afms135/signl/Hardware/Render_back.png

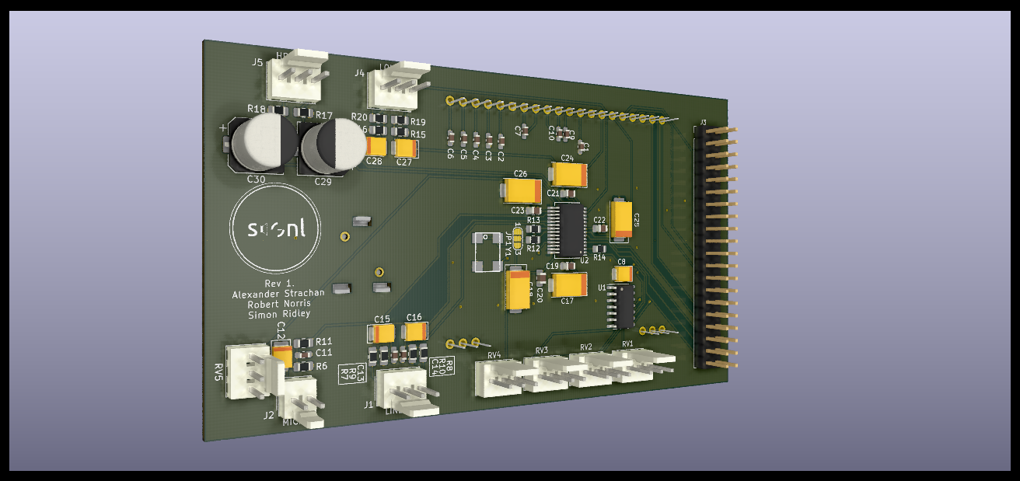
Hardware/Render_back.png
