afms135/signl/Hardware/Render_front.png

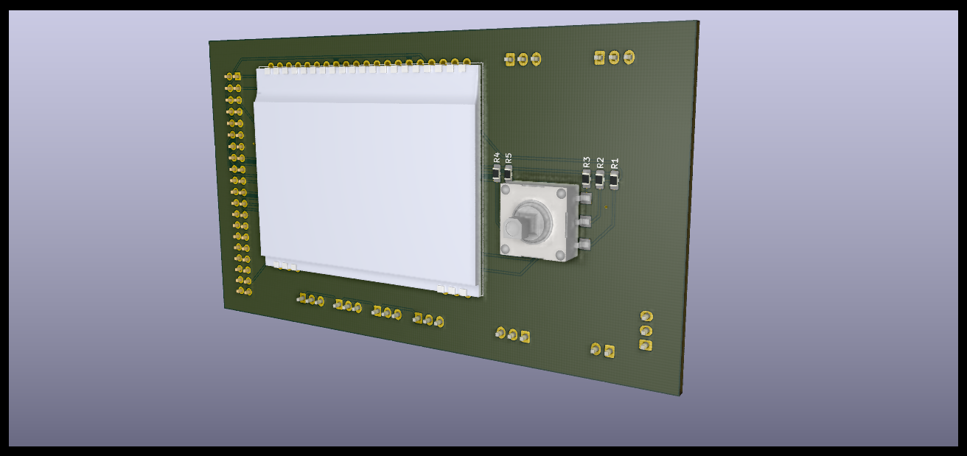
Hardware/Render_front.png
