afms135/signl/Hardware/RenderBackPerp.png

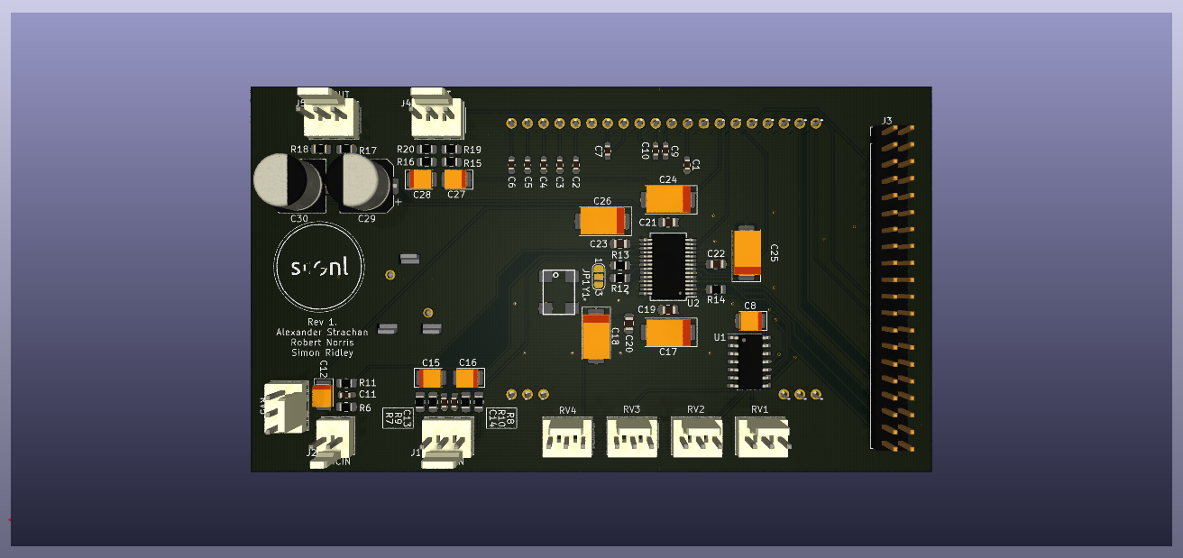
Hardware/RenderBackPerp.png
