afms135/signl/Hardware/RenderFrontPerp.png

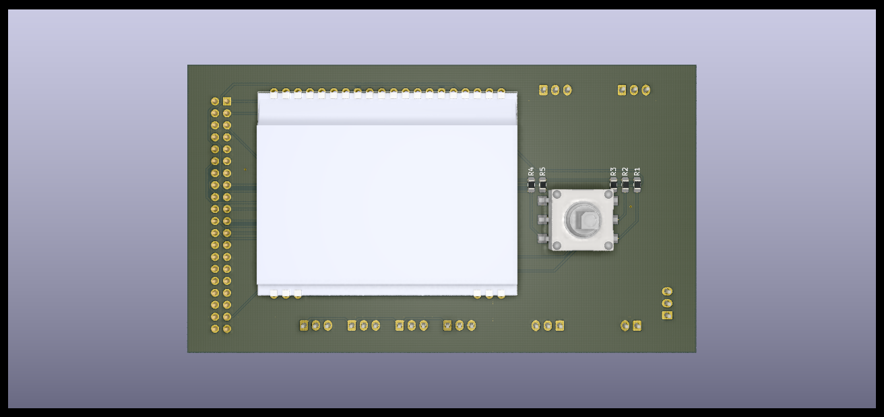
Hardware/RenderFrontPerp.png
