afms135/signl/Media/audio_interface.png

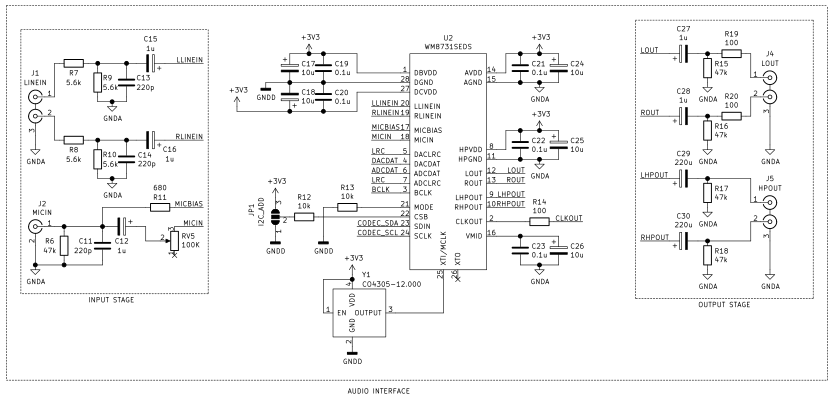
Media/audio_interface.png
