afms135/signl/Media/BlockDiagram.png

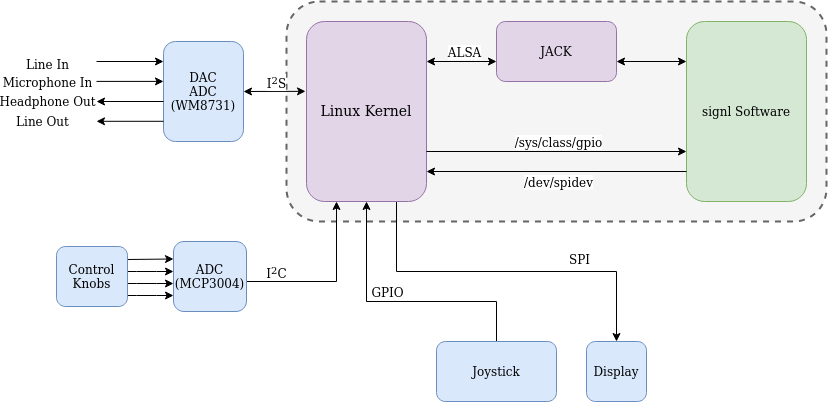
Media/BlockDiagram.png
