afms135/signl/Media/BoxRender.png

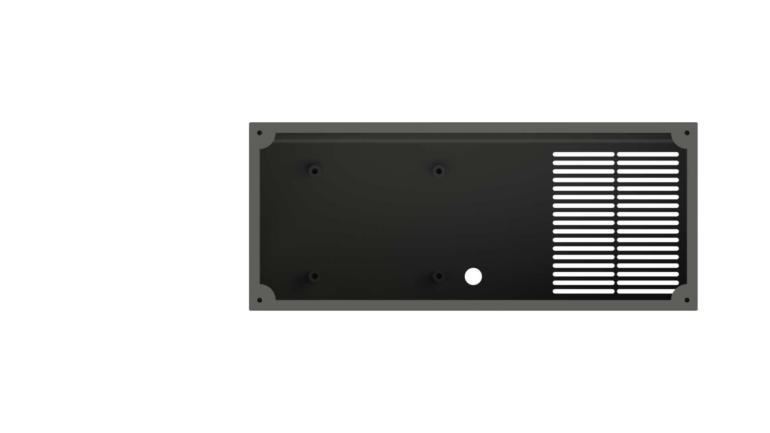
Media/BoxRender.png
