afms135/signl/Media/class_diag.png

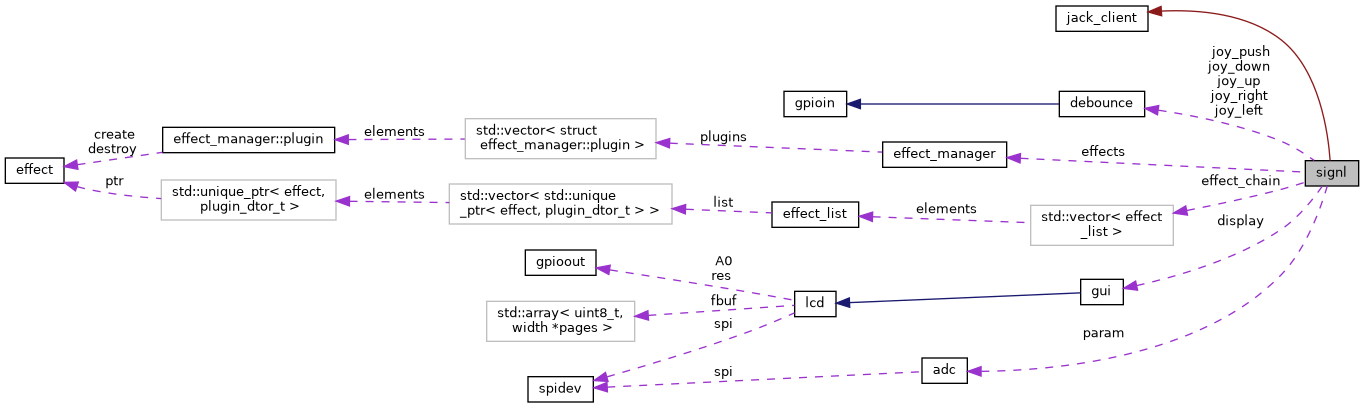
Media/class_diag.png
