afms135/signl/Media/effect_chain.png

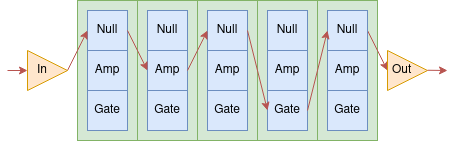
Media/effect_chain.png
