afms135/signl/Media/eqgraph.png

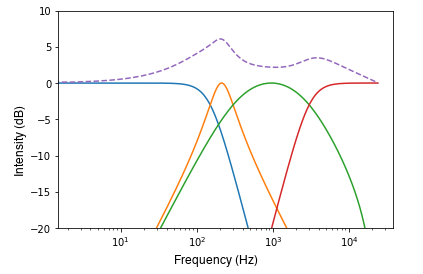
Media/eqgraph.png
