afms135/signl/Media/faceplate_dimensions.png

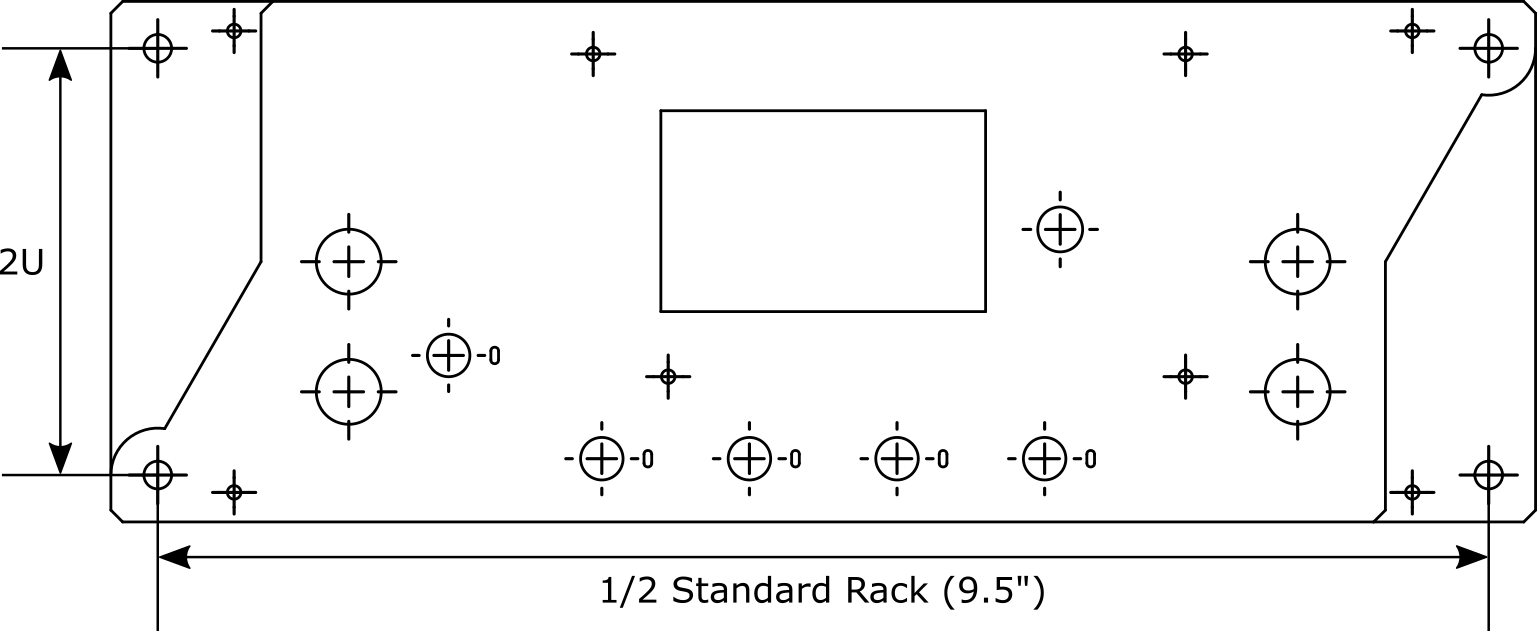
Media/faceplate_dimensions.png
