afms135/signl/Media/FullRender.png

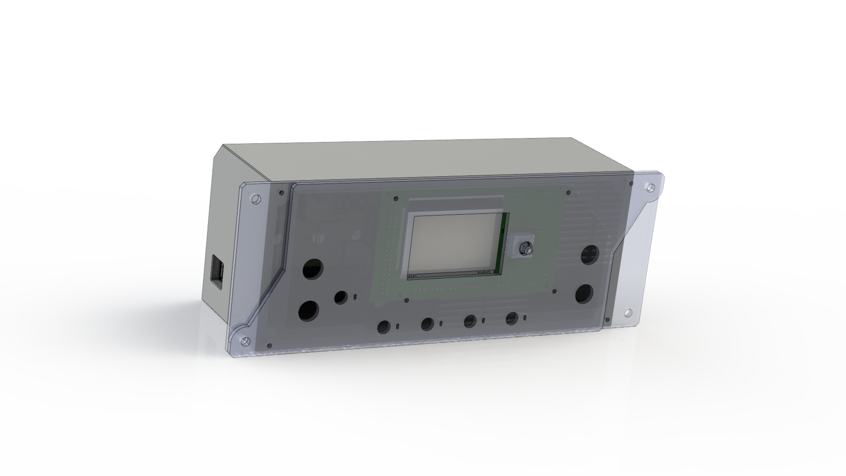
Media/FullRender.png
