afms135/signl/Media/gui_photos.jpg

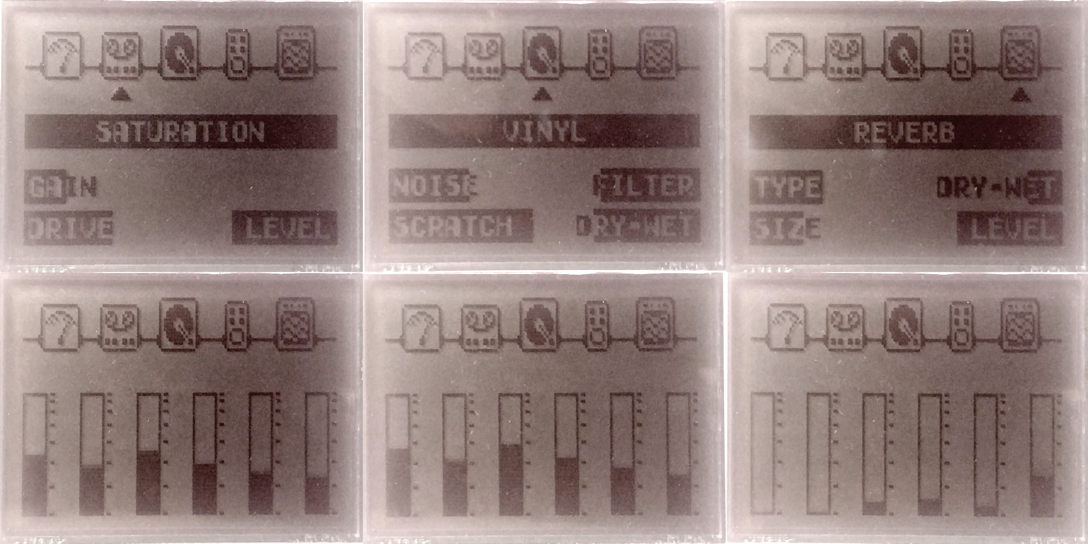
Media/gui_photos.jpg
