afms135/signl/Media/human_interface.png

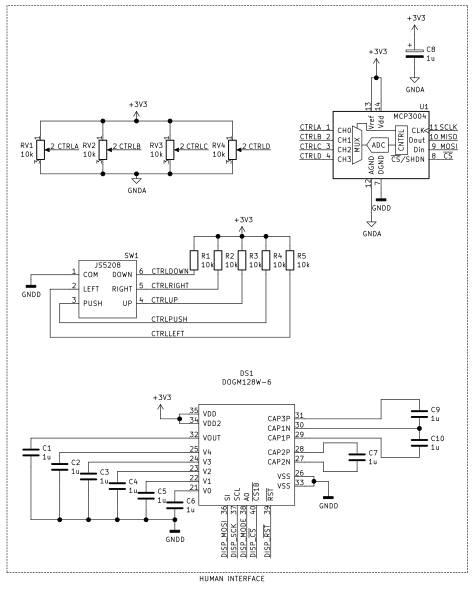
Media/human_interface.png
