afms135/signl/Media/Latencytest1.png

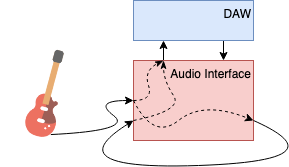
Media/Latencytest1.png
