afms135/signl/Media/Latencytest2.png

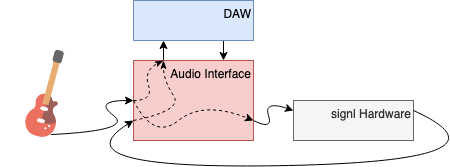
Media/Latencytest2.png
