afms135/signl/Media/PCBreal.jpeg

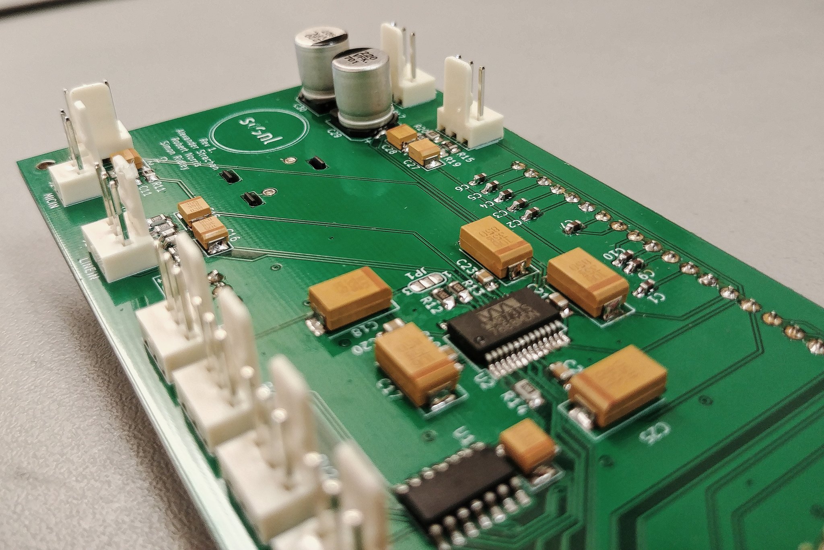
Media/PCBreal.jpeg
