afms135/signl/Media/PCBreal_front.jpeg

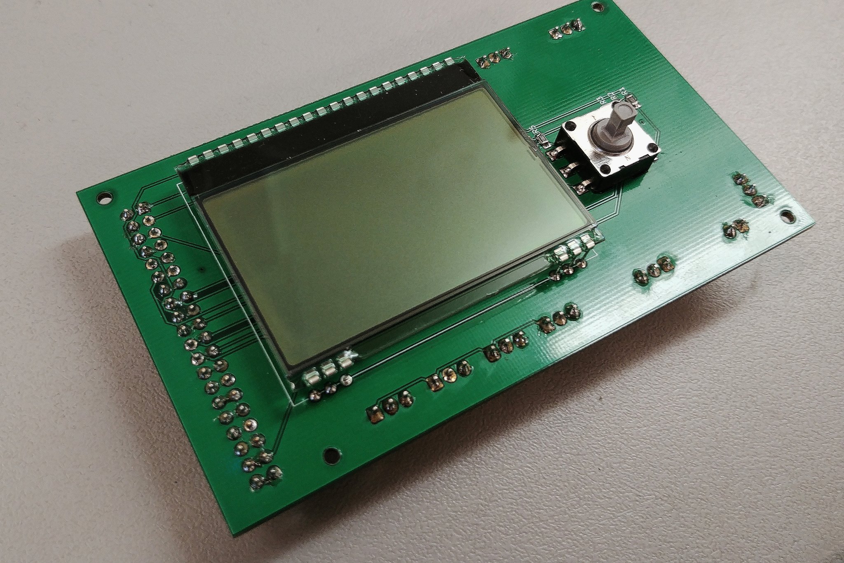
Media/PCBreal_front.jpeg
