afms135/signl/Media/software.png

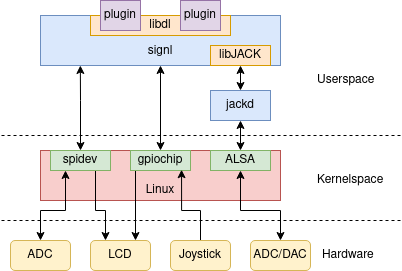
Media/software.png
