afms135/signl/Media/Video Thumbnails/eq.png

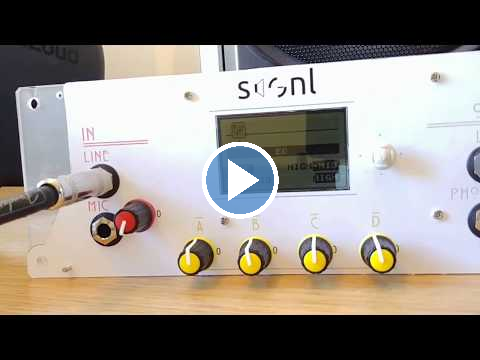
Media/Video Thumbnails/eq.png
