afms135/signl/Media/Video Thumbnails/guitartrack.png

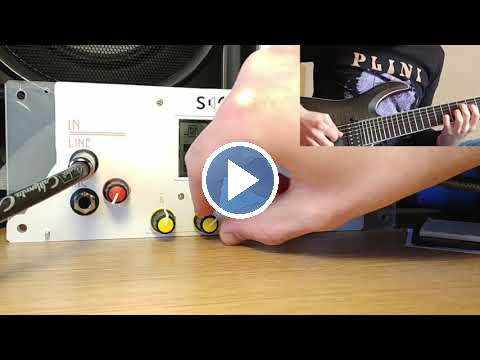
Media/Video Thumbnails/guitartrack.png
