afms135/signl/Media/Video Thumbnails/lofi.png

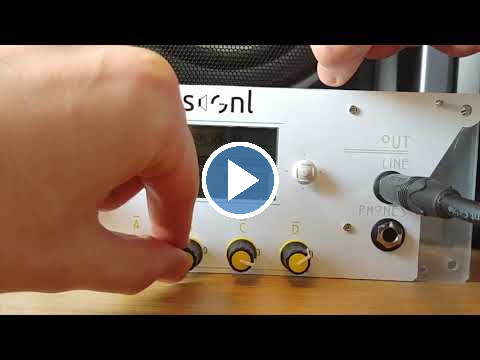
Media/Video Thumbnails/lofi.png
