afms135/signl/Media/Video Thumbnails/naivetuner.png

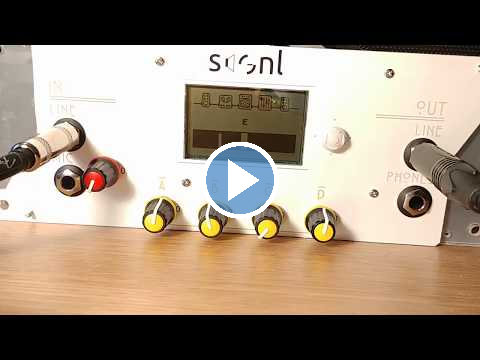
Media/Video Thumbnails/naivetuner.png
