afms135/signl/Media/Video Thumbnails/reverb.png

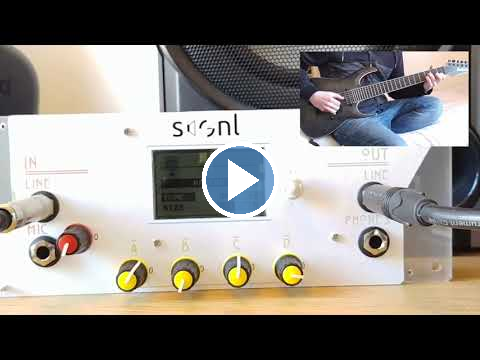
Media/Video Thumbnails/reverb.png
