afms135/signl/Media/Video Thumbnails/saturation.png

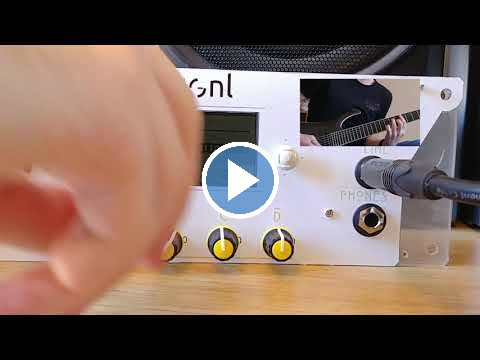
Media/Video Thumbnails/saturation.png
