afms135/signl/Media/Video Thumbnails/tremolo.png

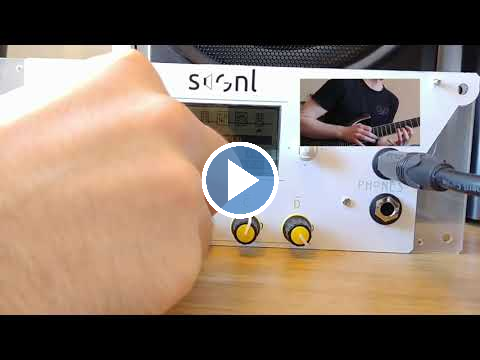
Media/Video Thumbnails/tremolo.png
