afms135/signl/Media/Video Thumbnails/tuner.png

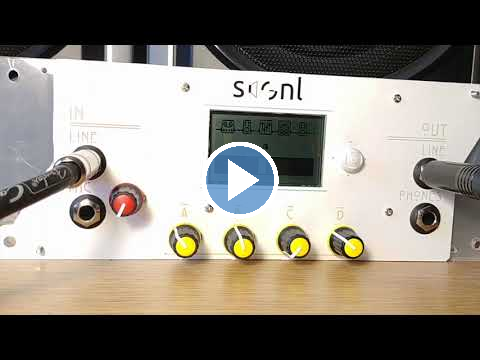
Media/Video Thumbnails/tuner.png
