afms135/signl/Media/Video Thumbnails/vinyl.png

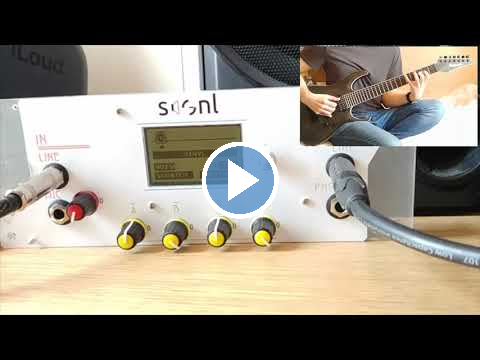
Media/Video Thumbnails/vinyl.png
