afms135/signl/Media/MidAssembly.jpg

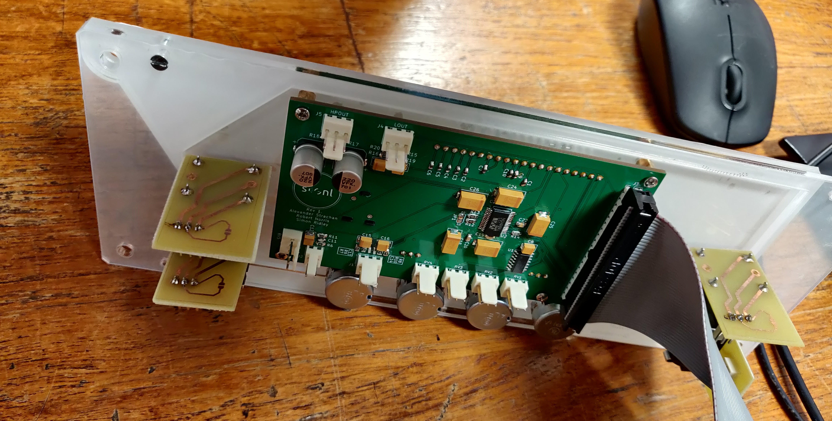
Media/MidAssembly.jpg
