afms135/signl/Media/Testing/Noise Gate/A.png

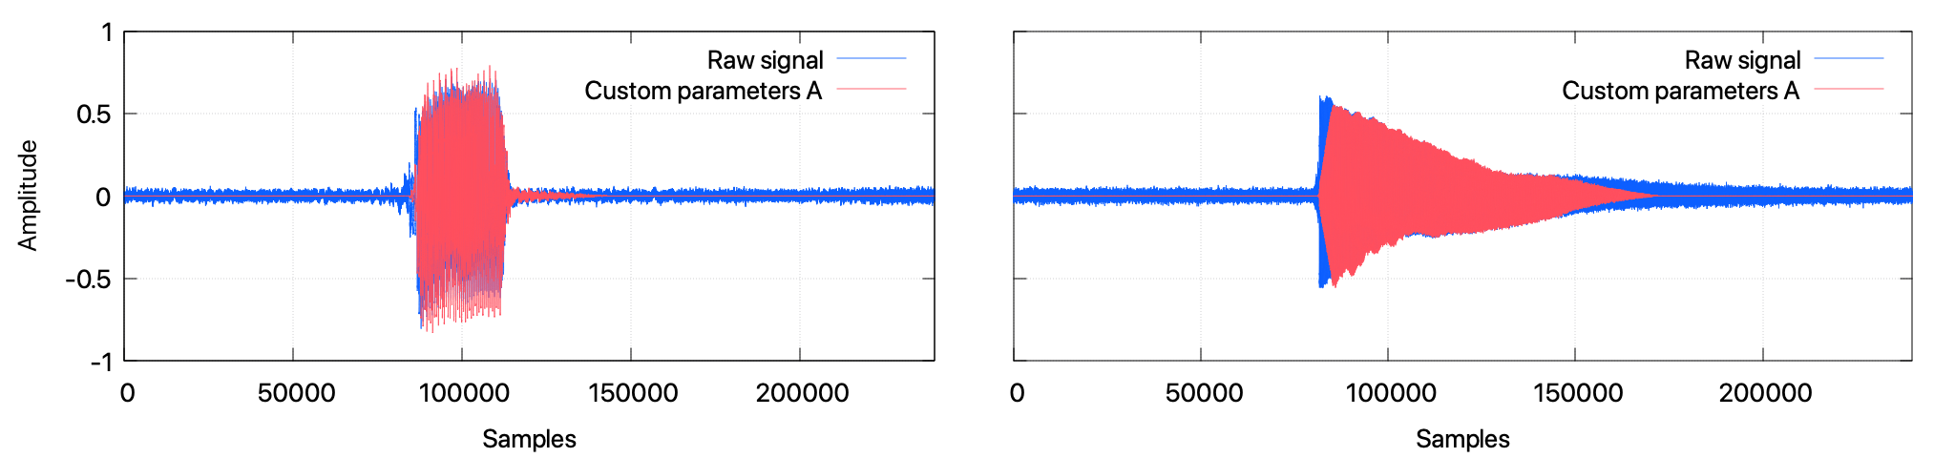
Media/Testing/Noise Gate/A.png
