afms135/signl/Media/Testing/Noise Gate/RAW.png

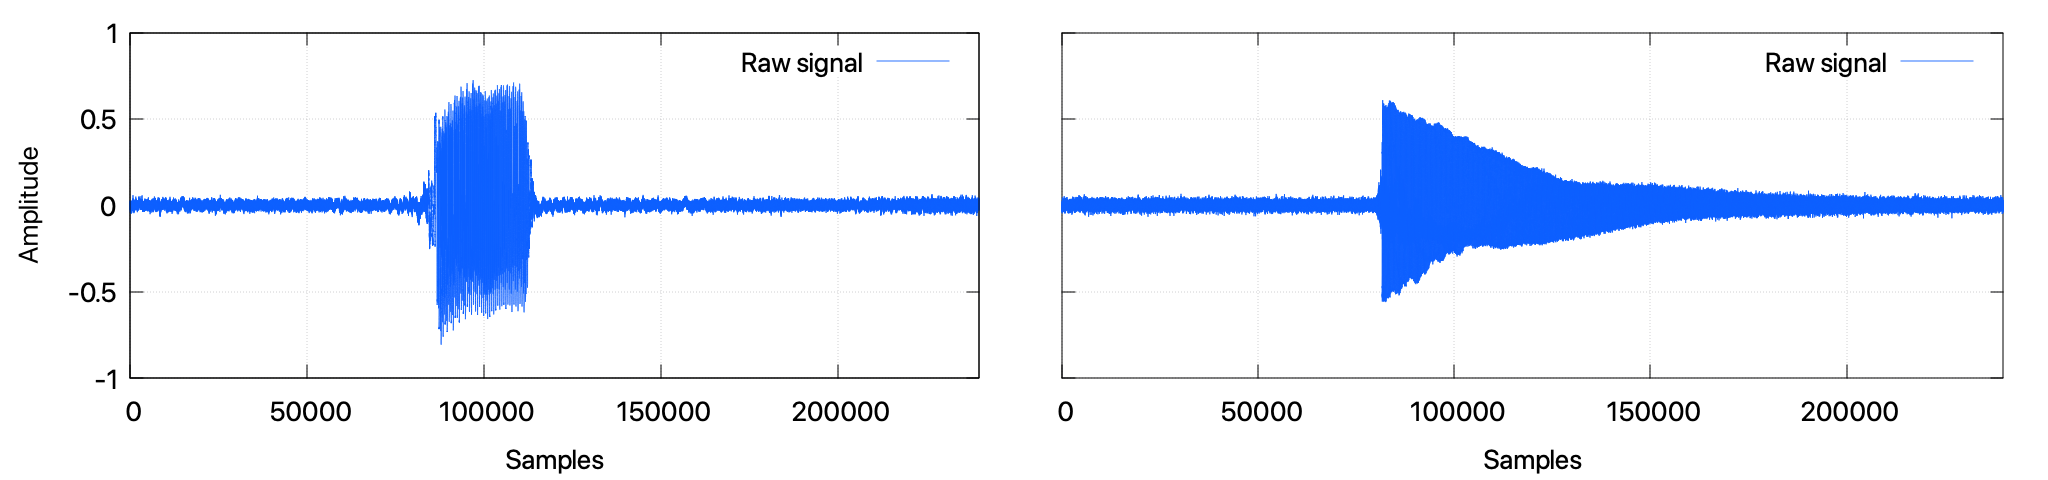
Media/Testing/Noise Gate/RAW.png
