afms135/signl/Media/Testing/Overdrive/Guitar2.png

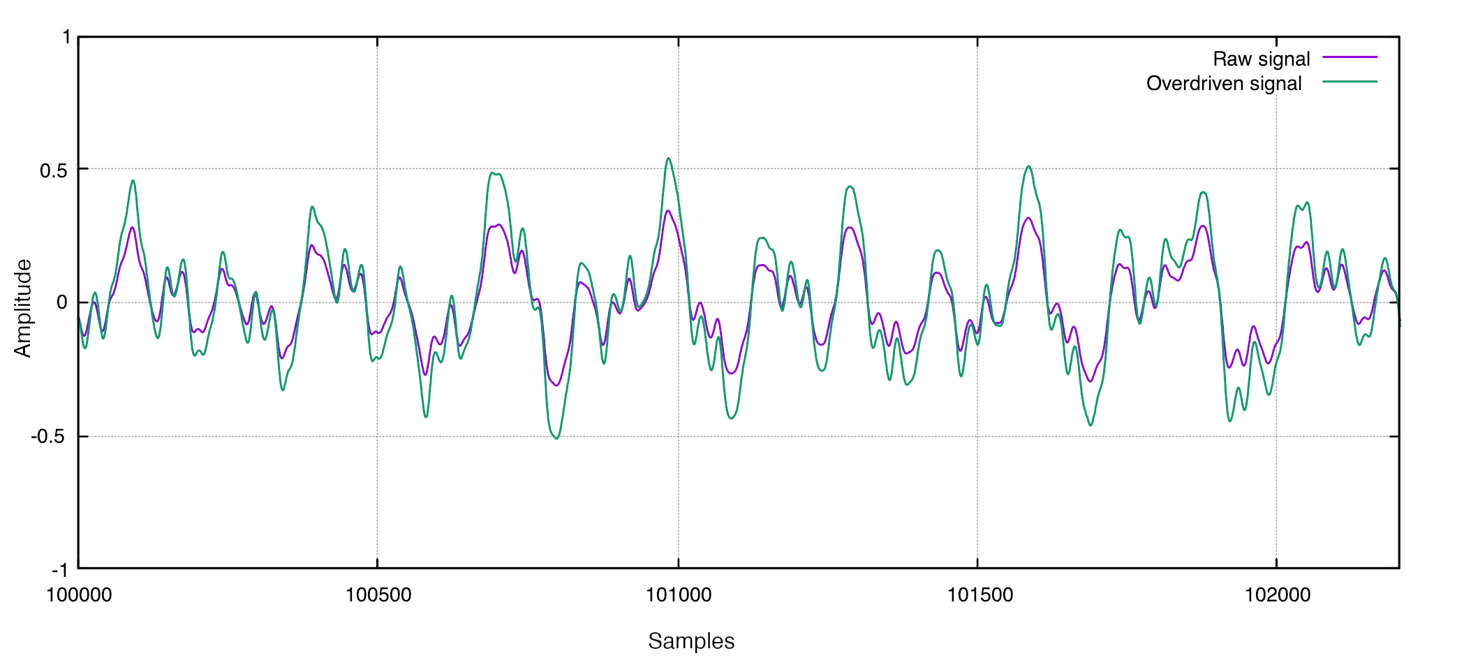
Media/Testing/Overdrive/Guitar2.png
