afms135/signl/Media/Testing/Overdrive/Guitar3.png

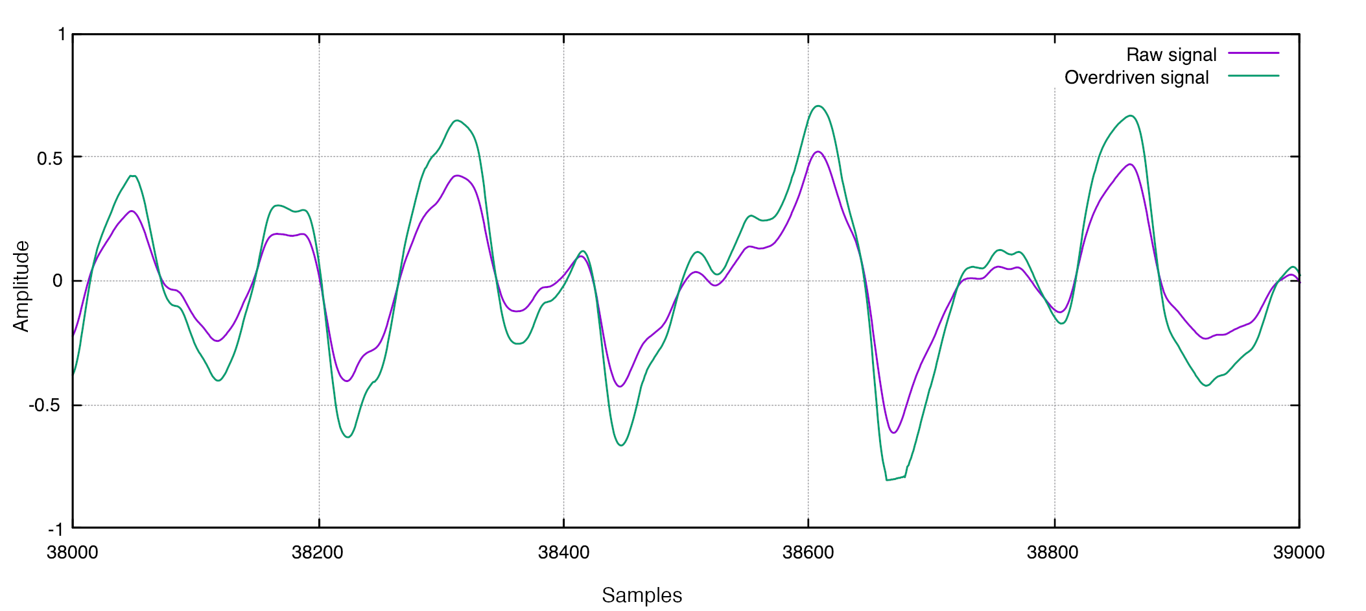
Media/Testing/Overdrive/Guitar3.png
