afms135/signl/Media/Testing/Overdrive/Sine.png

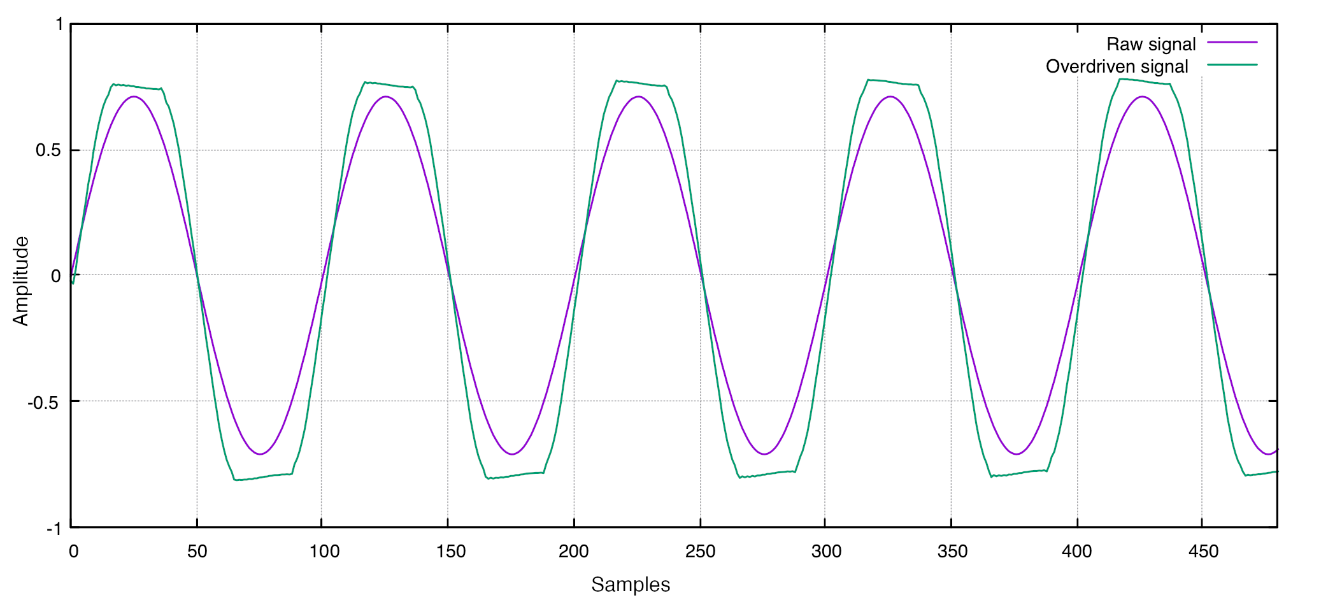
Media/Testing/Overdrive/Sine.png
