afms135/signl/Media/Testing/Reverb/Type1.png

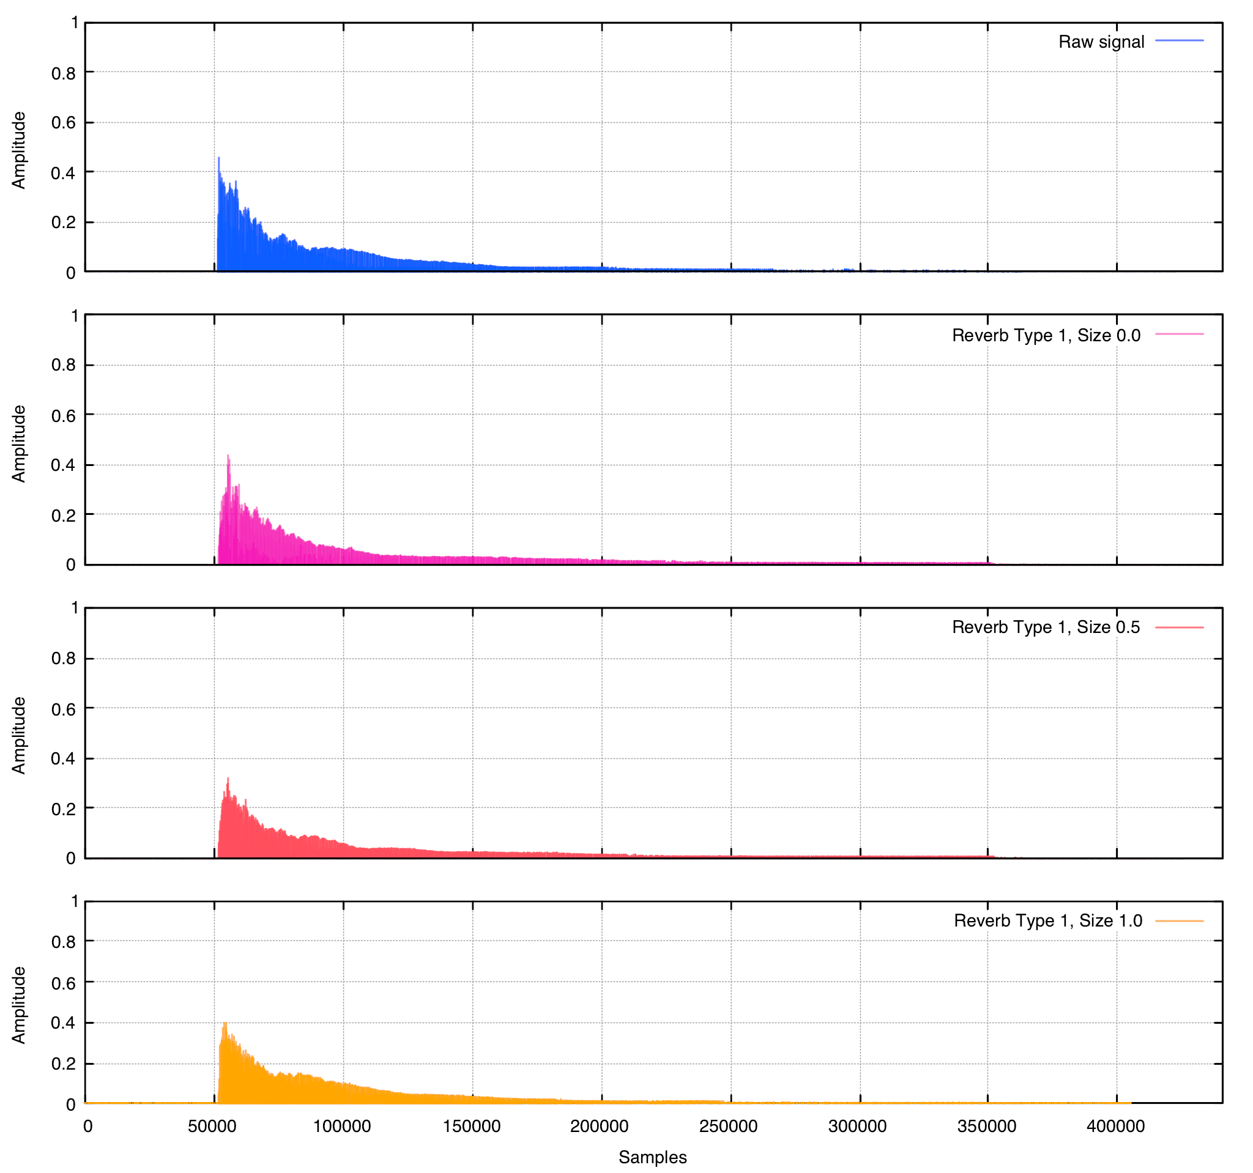
Media/Testing/Reverb/Type1.png
