afms135/signl/Media/Testing/Reverb/Type3.png

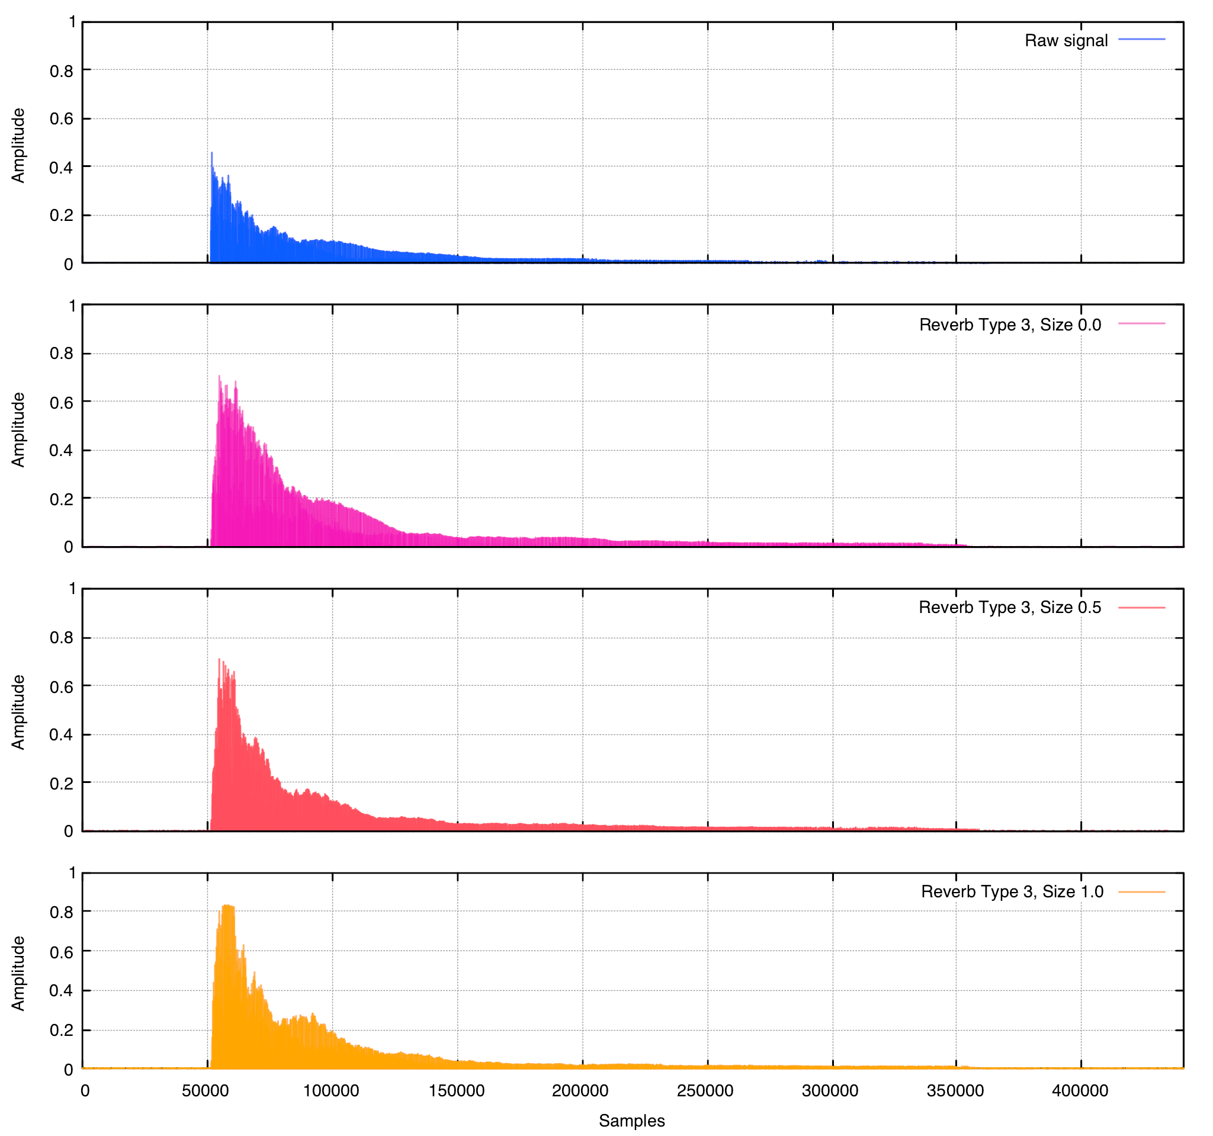
Media/Testing/Reverb/Type3.png
