afms135/signl/Media/Testing/Reverb/Type4.png

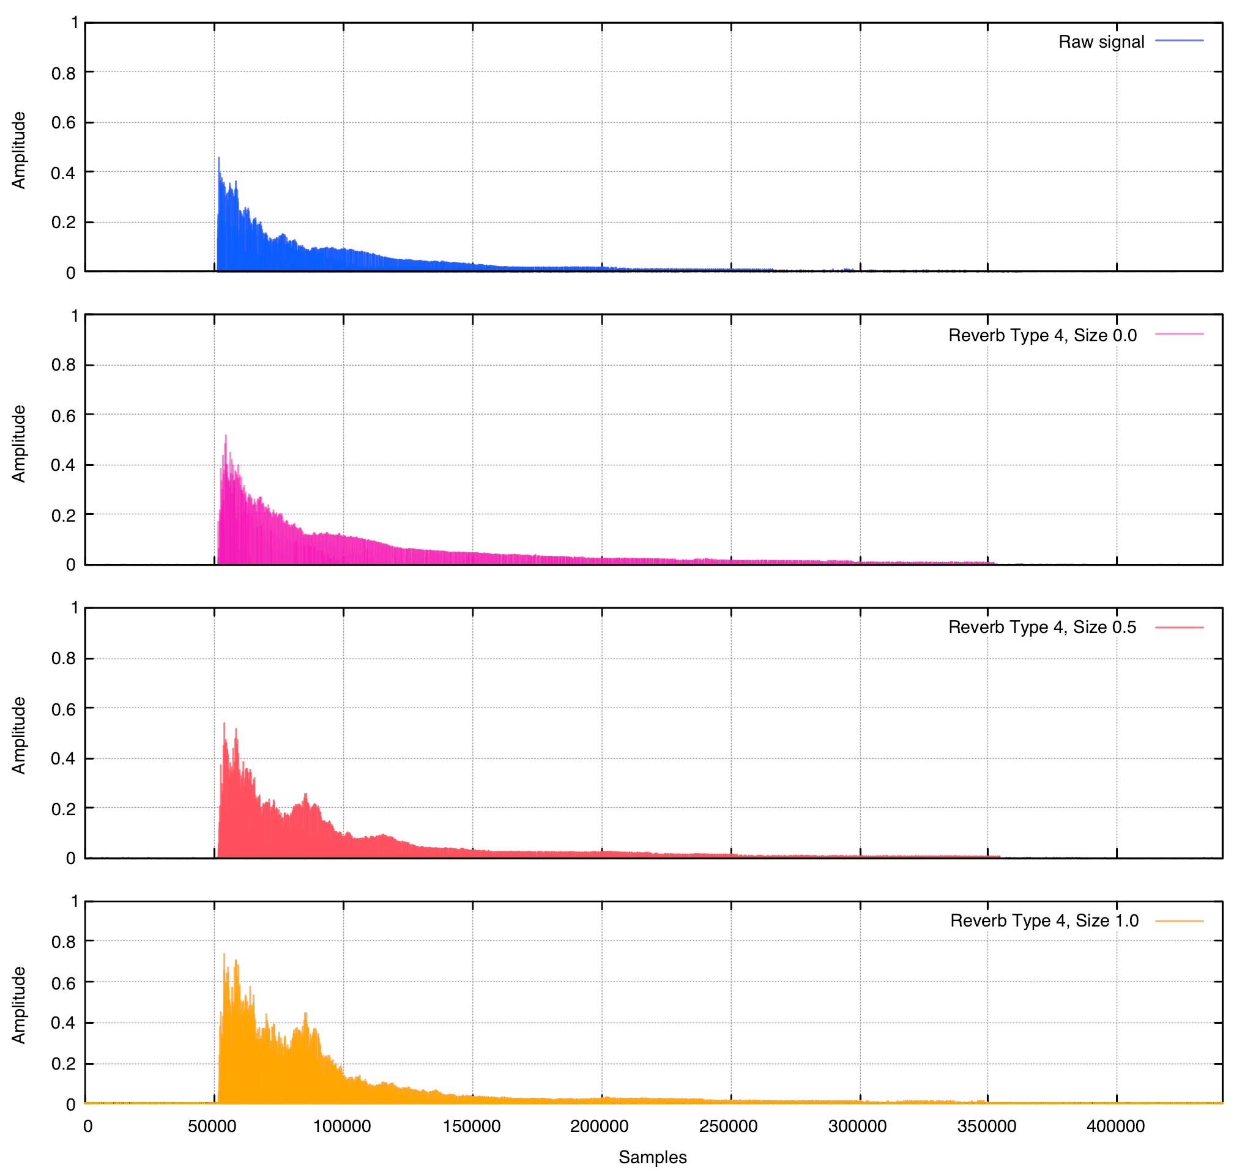
Media/Testing/Reverb/Type4.png
