afms135/signl/Media/Testing/Reverb/Type5.png

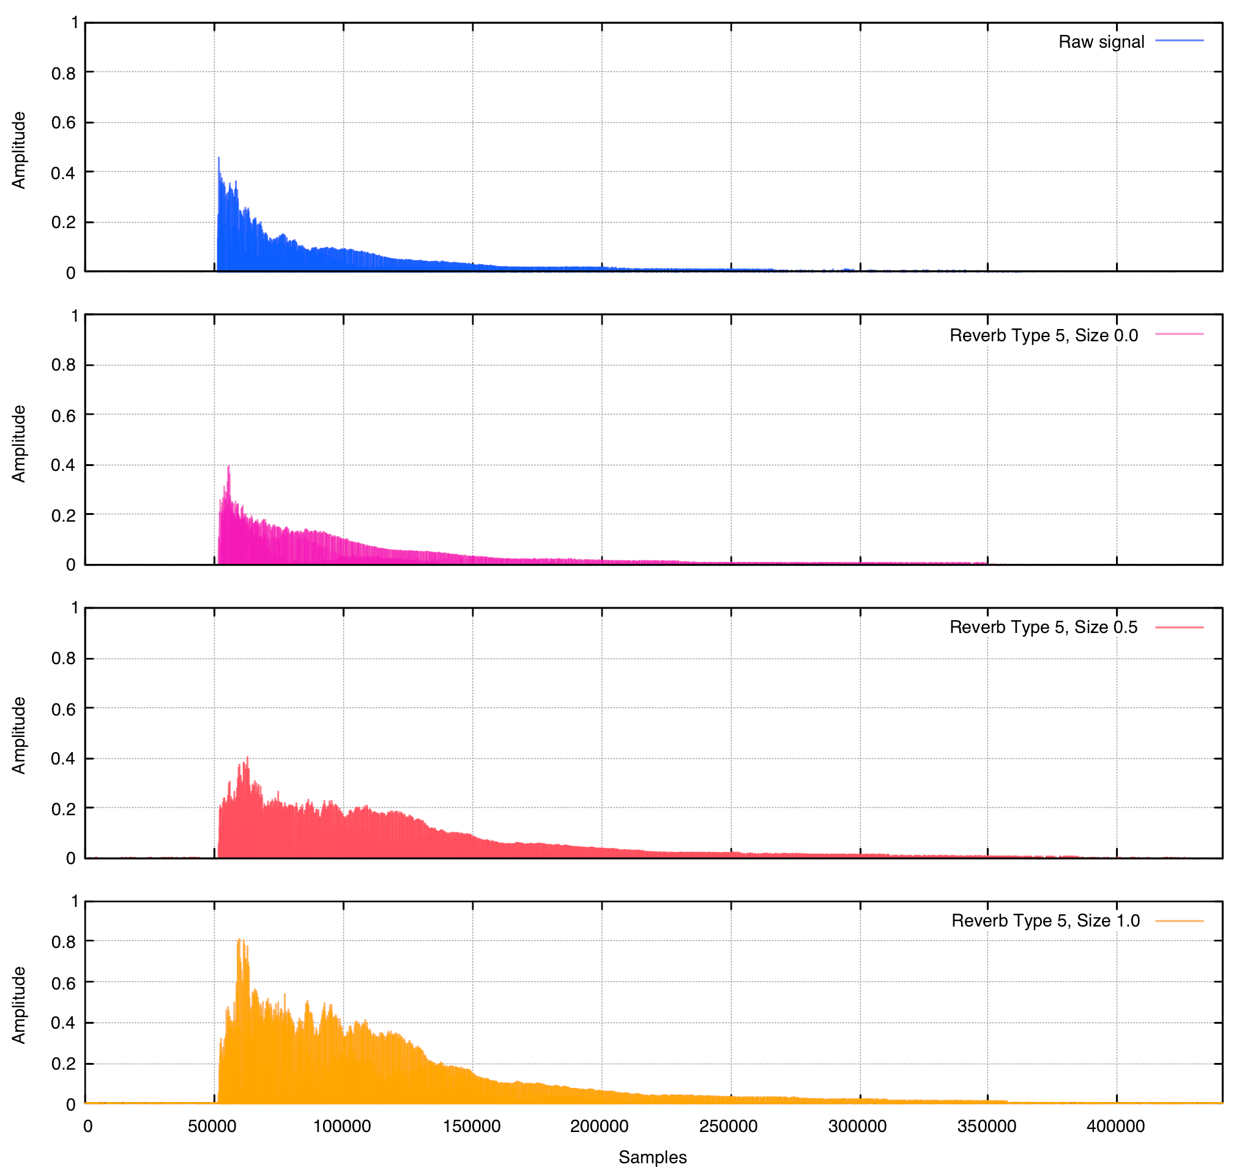
Media/Testing/Reverb/Type5.png
